emilorisit/hioa-eng-electronics/fritzing/VOLTAGE SENSING RELAY_etch_silk_bottom.pdf

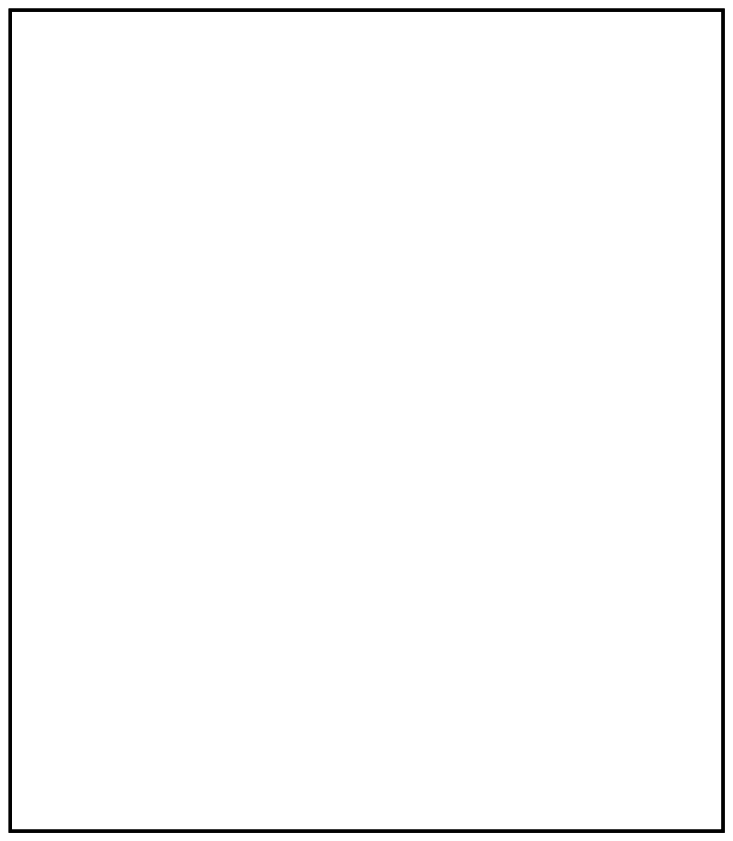
[picture p32: page 1]
