emilorisit/hioa-eng-electronics/fritzing/VOLTAGE SENSING RELAY_etch_silk_bottom_mirror.pdf

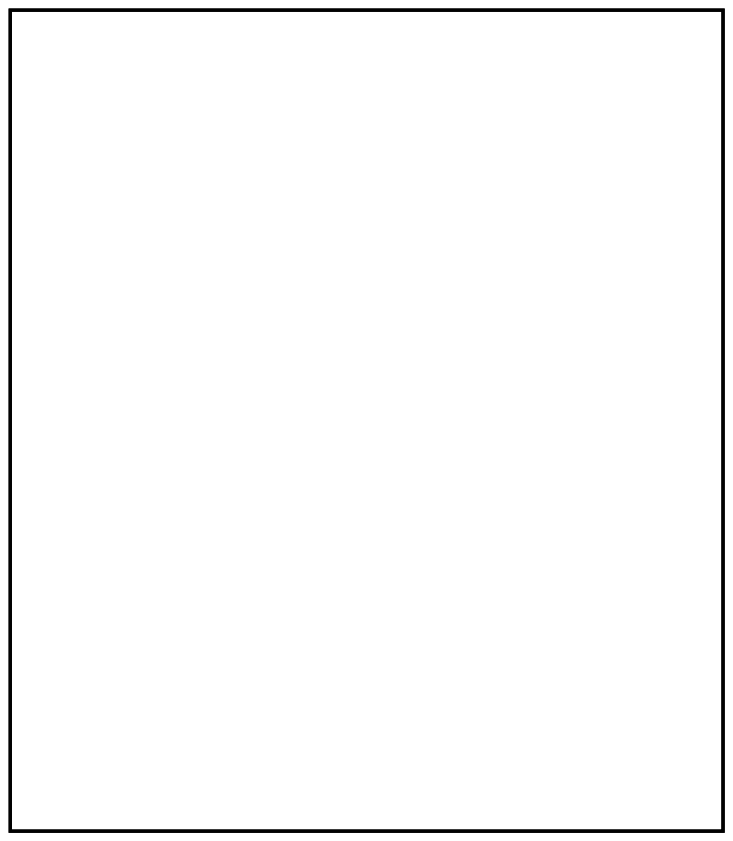
[picture p33: page 1]
