emilorisit/hioa-eng-electronics/fritzing/VOLTAGE SENSING RELAY_etch_silk_top.pdf

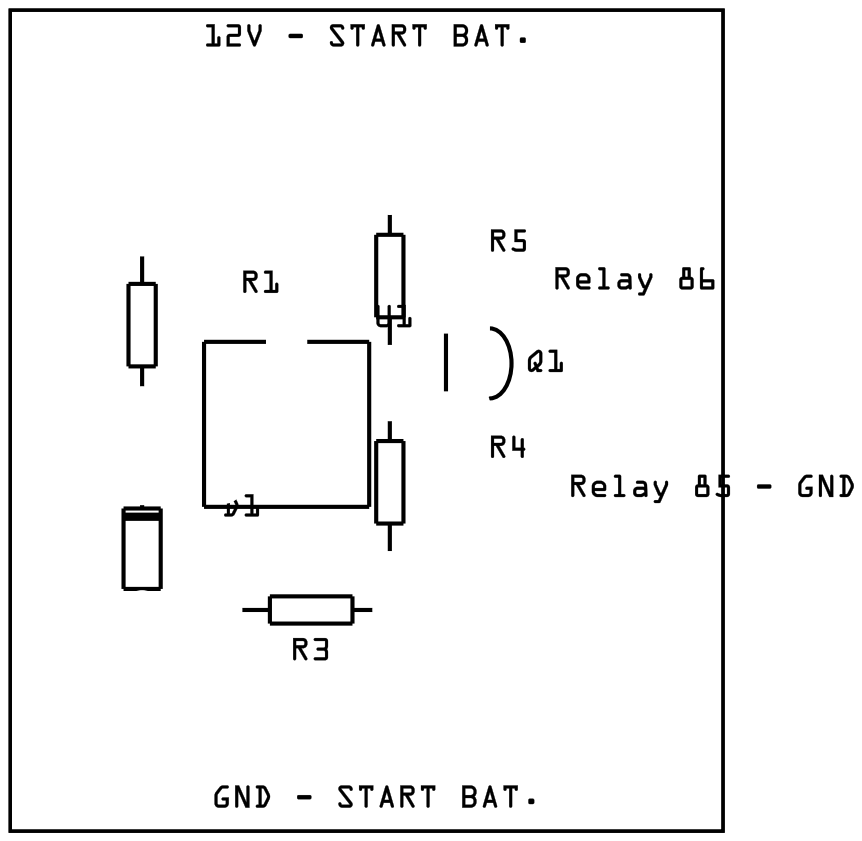
[picture p34: page 1]
