emilorisit/hioa-eng-electronics/fritzing/VOLTAGE SENSING RELAY_etch_silk_top_mirror.pdf

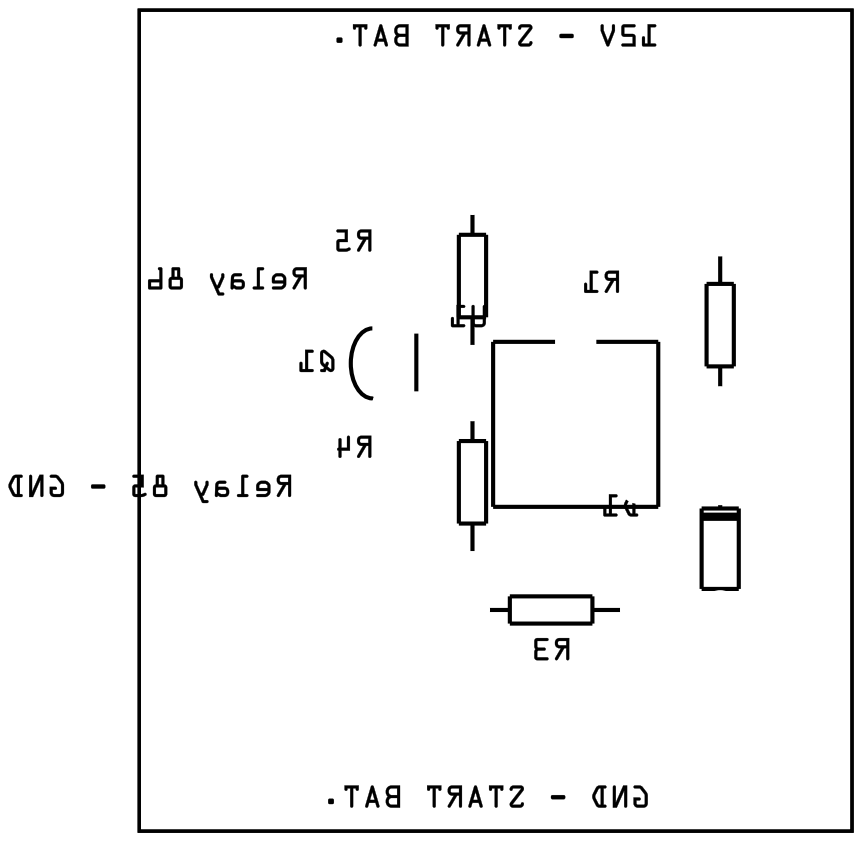
[picture p35: page 1]
