emilorisit/hioa-eng-electronics/eagle/2013-09-22-Start.sch

## EAGLE design eagle/2013-09-22-Start.sch (2025-01-27)

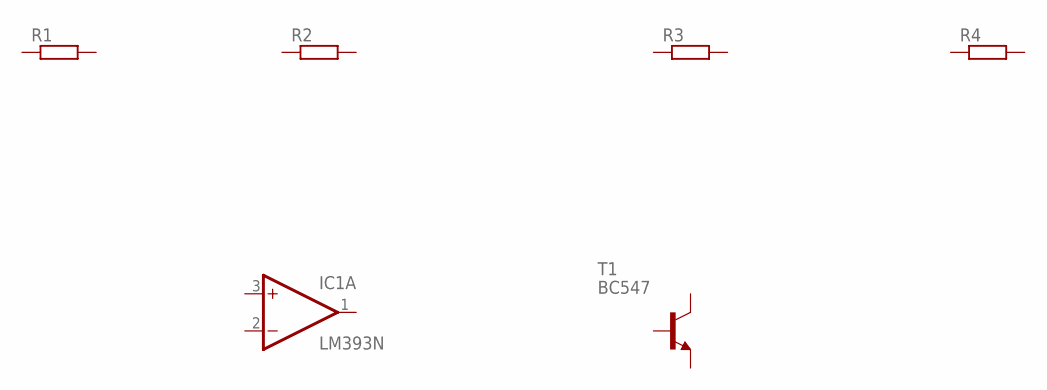
[picture p36: schematic 2013-09-22-Start.sch]

Parts:
IC1: LM393N; DIL08
R1, R2, R3, R4: R-EU_0207/7; 0207/7
T1: BC547; TO92
