emilorisit/hioa-eng-electronics/code/gpsknots/gpsknots.ino

#include <TinyGPS++.h>
#include <SoftwareSerial.h>

static const int RXPin = 2, TXPin = 3;
static const int GPSBaud = 4800;

// The TinyGPS++ object
TinyGPSPlus gps;

// The serial connection to the GPS device
SoftwareSerial ss(RXPin, TXPin);

void setup()
{
  Serial.begin(115200);
  ss.begin(GPSBaud);

}

void loop()
{

  //  printFloat(gps.speed.knots(), gps.speed.isValid(), 6, 2);


  Serial.println(gps.speed.knots());
  smartDelay(1000);

  if (millis() > 5000 && gps.charsProcessed() < 10)
    Serial.println(F("No GPS data received: check wiring"));
}


static void smartDelay(unsigned long ms)
{
  unsigned long start = millis();
  do 
  {
    while (ss.available())
      gps.encode(ss.read());
  } 
  while (millis() - start < ms);
}
